nicholashuyhoang/rdc-water-sensor/WaterSensor.asc

Q1: npn; 2N3904
R1: res; 3.3k
R2: res; 330k
Vs: voltage; 5V
Named nets: 0, Vout
.tran 0 0.1s 0
3.3V Max
